Ente004/RobOHMobil-convoy/Dokumentation/KiCad-Pläne/Robomobil_ESP.kicad_sch

## KiCad design Dokumentation/KiCad-Pläne/Robomobil_ESP.kicad_sch (2026-03-16)

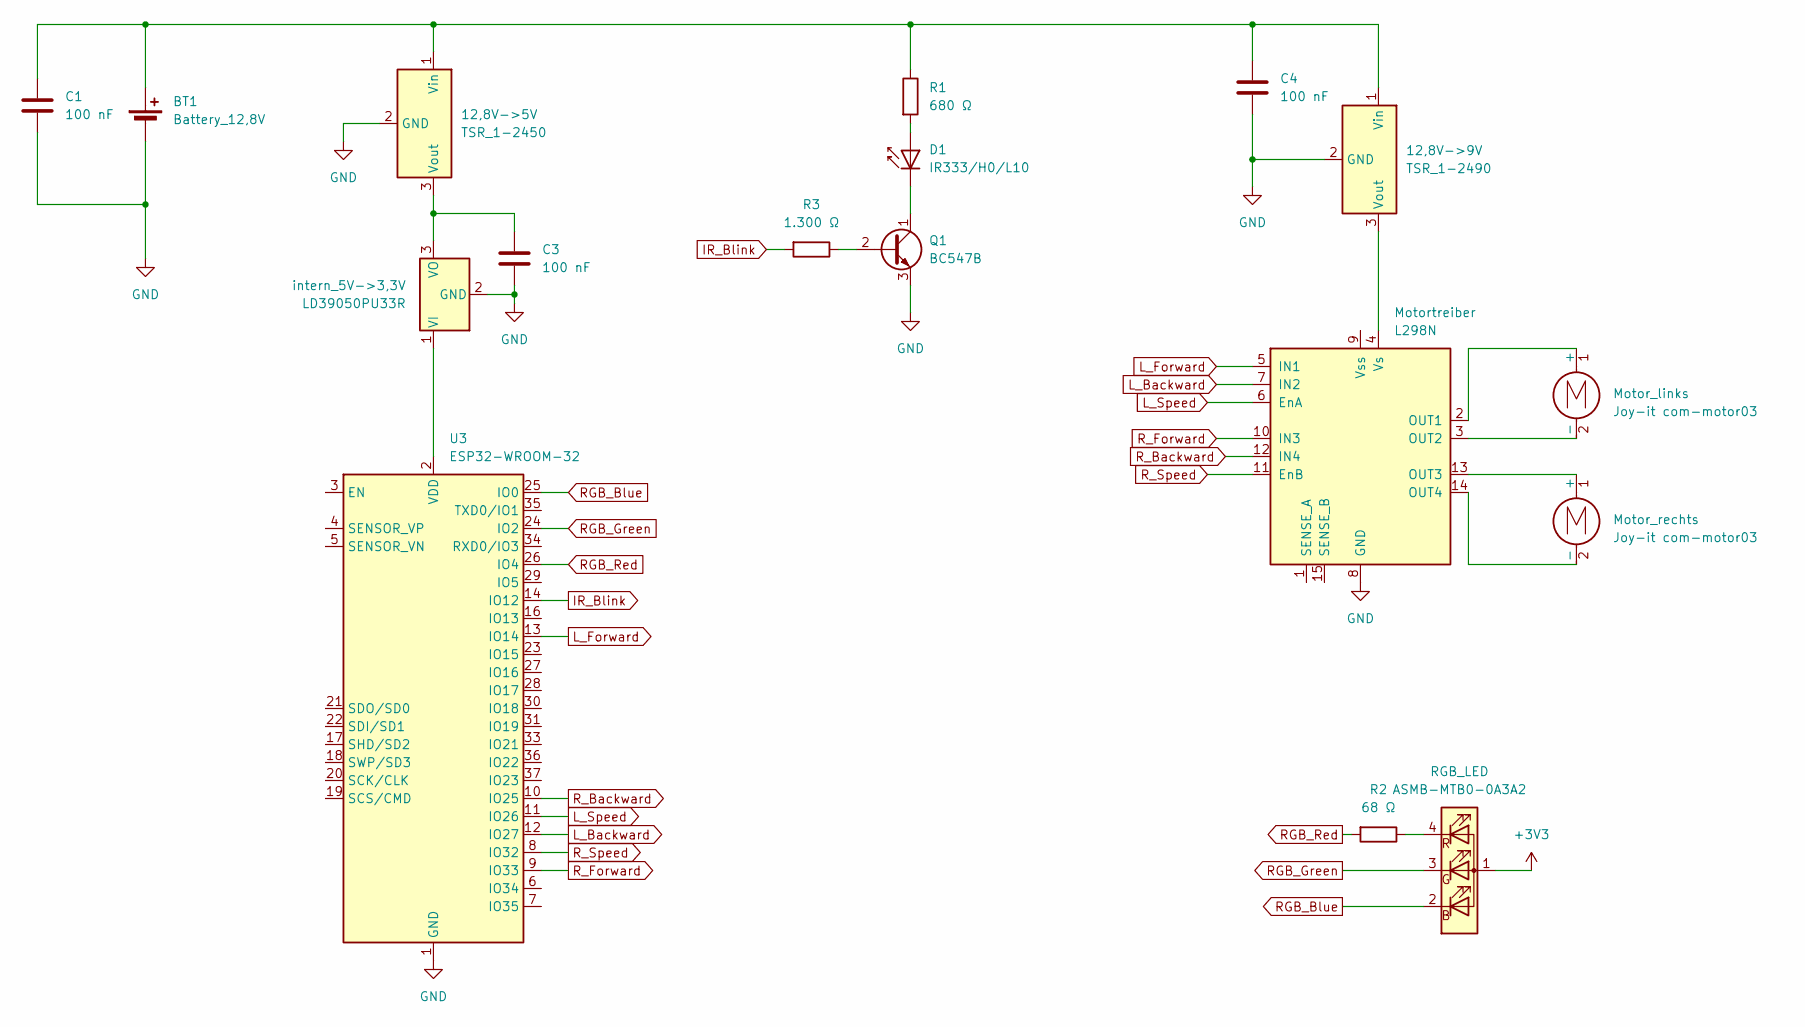
[picture p24: schematic Robomobil_ESP.kicad_sch]

Parts:
12,8V->5V: TSR_1-2450; Converter_DCDC_TRACO_TSR-1_THT
12,8V->9V: TSR_1-2490; Converter_DCDC_TRACO_TSR-1_THT
BT1: Battery_12,8V
C1, C3, C4: 100 nF
D1: IR333/H0/L10; LED_D5.0mm_IRGrey
Motor_links: Joy-it com-motor03
Motor_rechts: Joy-it com-motor03
Motortreiber: L298N; TO-220-15_P2.54x2.54mm_StaggerOdd_Lead4.58mm_Vertical
Q1: BC547B; TO-92_Inline
R1: 680 Ω
R2: 68 Ω
R3: 1.300 Ω
RGB_LED: ASMB-MTB0-0A3A2; LED_Avago_PLCC4_3.2x2.8mm_CW
U3: ESP32-WROOM-32
intern_5V->3,3V: LD39050PU33R; TO-252-3_TabPin2

Connections:
+3V3: RGB_LED.1 (A)
GND: 12,8V->5V.2 (GND), 12,8V->9V.2 (GND), BT1.2 (-), C1.2, C3.2, C4.2, Motortreiber.8 (GND), Q1.3 (E), U3.1 (GND), U3.15 (GND), U3.38 (GND), U3.39 (GND), intern_5V->3,3V.2 (GND)
IR_Blink: R3.2, U3.14 (IO12)
L_Backward: Motortreiber.7 (IN2), U3.12 (IO27)
L_Forward: Motortreiber.5 (IN1), U3.13 (IO14)
L_Speed: Motortreiber.6 (EnA), U3.11 (IO26)
unnamed: 12,8V->5V.1 (Vin), 12,8V->9V.1 (Vin), BT1.1 (+), C1.1, C4.1, R1.1
unnamed: 12,8V->5V.3 (Vout), C3.1, intern_5V->3,3V.3 (VO)
unnamed: 12,8V->9V.3 (Vout), Motortreiber.4 (Vs)
unnamed: D1.1 (K), Q1.1 (C)
unnamed: D1.2 (A), R1.2
unnamed: Motor_links.1 (+), Motortreiber.2 (OUT1)
unnamed: Motor_links.2 (-), Motortreiber.3 (OUT2)
unnamed: Motor_rechts.1 (+), Motortreiber.13 (OUT3)
unnamed: Motor_rechts.2 (-), Motortreiber.14 (OUT4)
unnamed: Q1.2 (B), R3.1
unnamed: R2.1, RGB_LED.4 (RK)
unnamed: U3.2 (VDD), intern_5V->3,3V.1 (VI)
RGB_Blue: RGB_LED.2 (BK), U3.25 (IO0)
RGB_Green: RGB_LED.3 (GK), U3.24 (IO2)
RGB_Red: R2.2, U3.26 (IO4)
R_Backward: Motortreiber.12 (IN4), U3.10 (IO25)
R_Forward: Motortreiber.10 (IN3), U3.9 (IO33)
R_Speed: Motortreiber.11 (EnB), U3.8 (IO32)
