Ente004/RobOHMobil-convoy/Dokumentation/KiCad-Pläne/Robomobil_STM.kicad_sch

## KiCad design Dokumentation/KiCad-Pläne/Robomobil_STM.kicad_sch (2026-03-16)

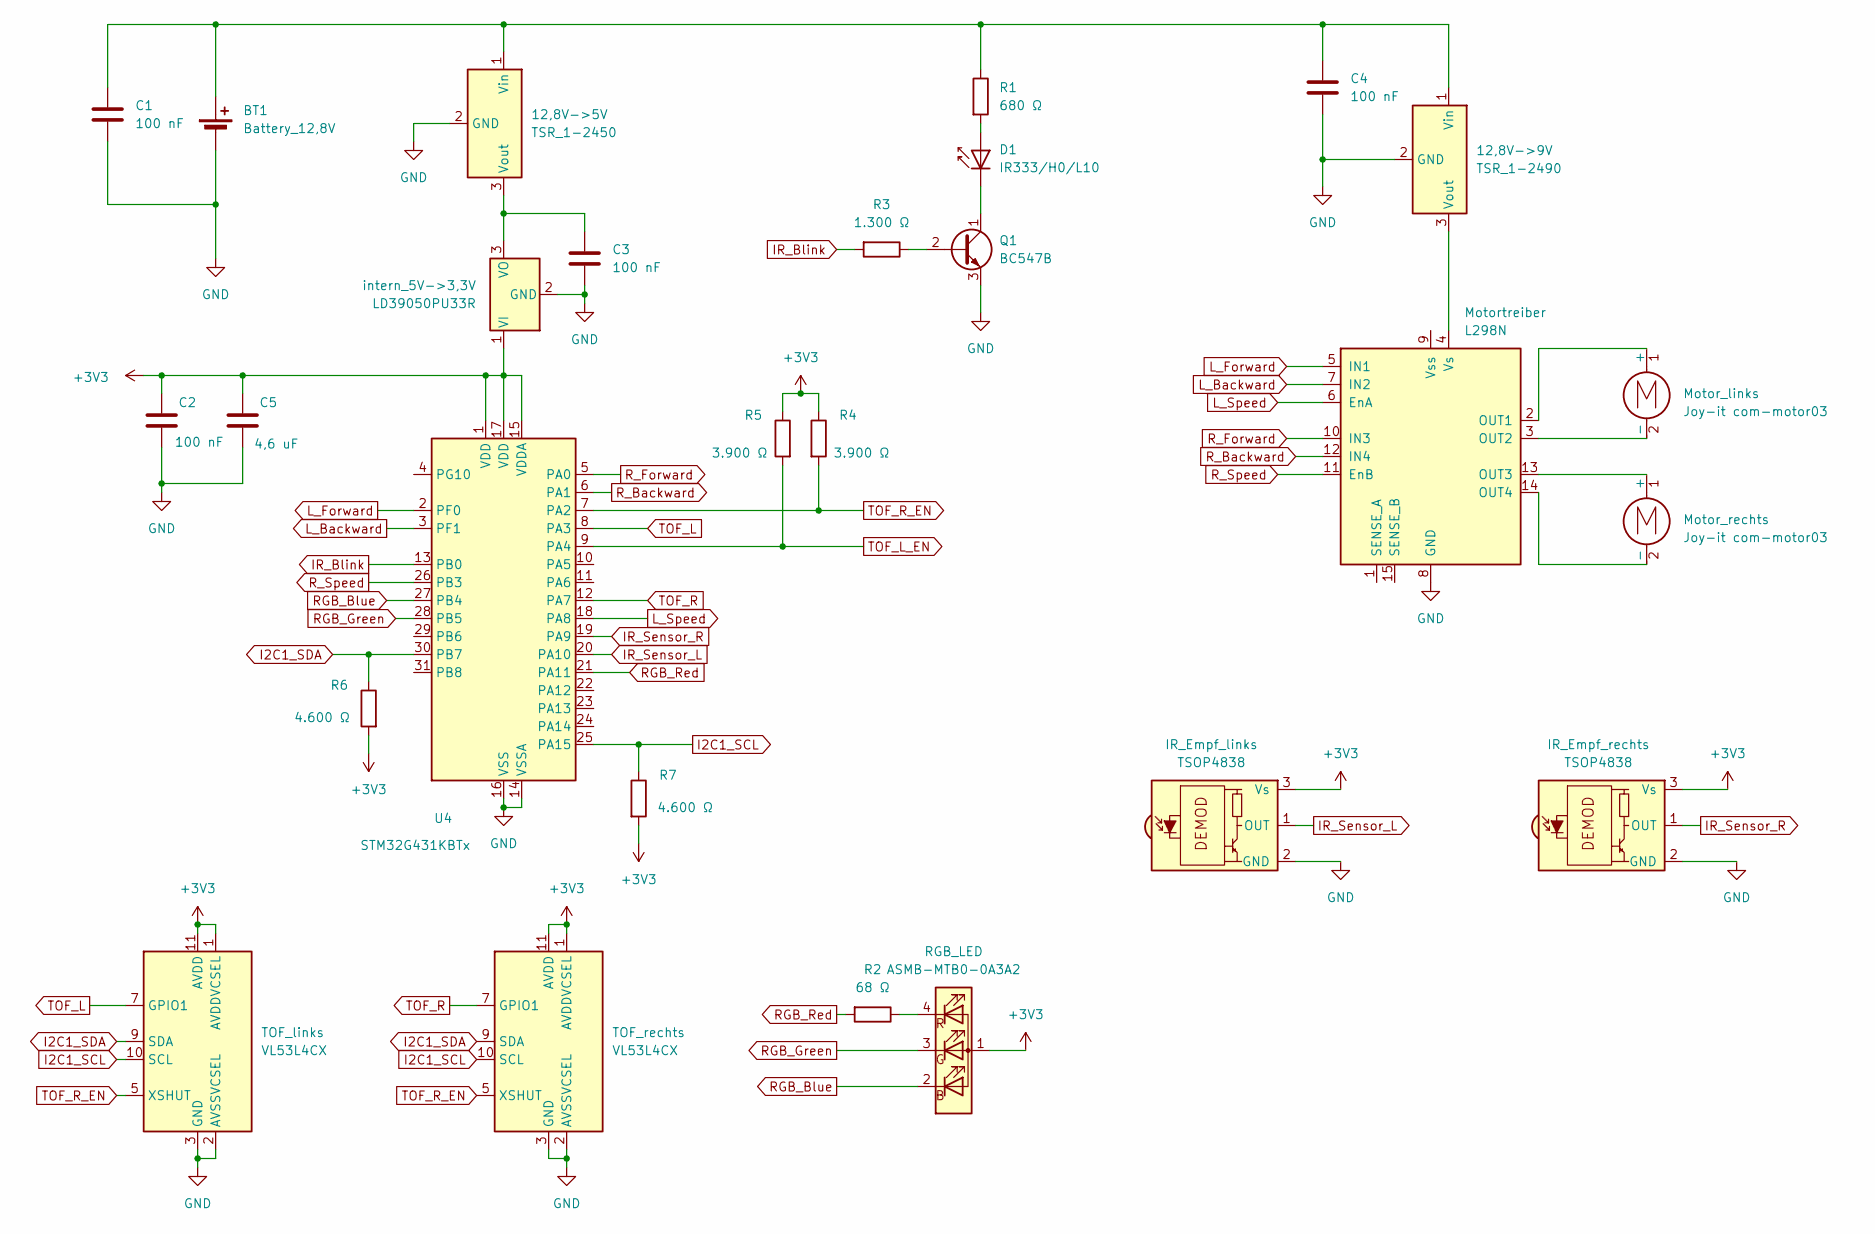
[picture p25: schematic Robomobil_STM.kicad_sch]

Parts:
12,8V->5V: TSR_1-2450; Converter_DCDC_TRACO_TSR-1_THT
12,8V->9V: TSR_1-2490; Converter_DCDC_TRACO_TSR-1_THT
BT1: Battery_12,8V
C1, C2, C3, C4: 100 nF
C5: 4,6 uF
D1: IR333/H0/L10; LED_D5.0mm_IRGrey
IR_Empf_links: TSOP4838; Vishay_MINIMOLD-3Pin
IR_Empf_rechts: TSOP4838; Vishay_MINIMOLD-3Pin
Motor_links: Joy-it com-motor03
Motor_rechts: Joy-it com-motor03
Motortreiber: L298N; TO-220-15_P2.54x2.54mm_StaggerOdd_Lead4.58mm_Vertical
Q1: BC547B; TO-92_Inline
R1: 680 Ω
R2: 68 Ω
R3: 1.300 Ω
R4, R5: 3.900 Ω
R6, R7: 4.600 Ω
RGB_LED: ASMB-MTB0-0A3A2; LED_Avago_PLCC4_3.2x2.8mm_CW
TOF_links: VL53L4CX; ST_VL53L1x
TOF_rechts: VL53L4CX; ST_VL53L1x
U4: STM32G431KBTx; LQFP-32_7x7mm_P0.8mm
intern_5V->3,3V: LD39050PU33R; TO-252-3_TabPin2

Connections:
+3V3: C2.1, C5.1, IR_Empf_links.3 (Vs), IR_Empf_rechts.3 (Vs), R4.1, R5.1, R6.2, R7.2, RGB_LED.1 (A), TOF_links.1 (AVDDVCSEL), TOF_links.11 (AVDD), TOF_rechts.1 (AVDDVCSEL), TOF_rechts.11 (AVDD), U4.1 (VDD), U4.15 (VDDA), U4.17 (VDD), intern_5V->3,3V.1 (VI)
GND: 12,8V->5V.2 (GND), 12,8V->9V.2 (GND), BT1.2 (-), C1.2, C2.2, C3.2, C4.2, C5.2, IR_Empf_links.2 (GND), IR_Empf_rechts.2 (GND), Motortreiber.8 (GND), Q1.3 (E), TOF_links.2 (AVSSVCSEL), TOF_links.3 (GND), TOF_links.4 (GND), TOF_links.6 (GND), TOF_links.12 (GND), TOF_rechts.2 (AVSSVCSEL), TOF_rechts.3 (GND), TOF_rechts.4 (GND), TOF_rechts.6 (GND), TOF_rechts.12 (GND), U4.14 (VSSA), U4.16 (VSS), U4.32 (VSS), intern_5V->3,3V.2 (GND)
I2C1_SCL: R7.1, TOF_links.10 (SCL), TOF_rechts.10 (SCL), U4.25 (PA15)
I2C1_SDA: R6.1, TOF_links.9 (SDA), TOF_rechts.9 (SDA), U4.30 (PB7)
IR_Blink: R3.2, U4.13 (PB0)
IR_Sensor_L: IR_Empf_links.1 (OUT), U4.20 (PA10)
IR_Sensor_R: IR_Empf_rechts.1 (OUT), U4.19 (PA9)
L_Backward: Motortreiber.7 (IN2), U4.3 (PF1)
L_Forward: Motortreiber.5 (IN1), U4.2 (PF0)
L_Speed: Motortreiber.6 (EnA), U4.18 (PA8)
unnamed: 12,8V->5V.1 (Vin), 12,8V->9V.1 (Vin), BT1.1 (+), C1.1, C4.1, R1.1
unnamed: 12,8V->5V.3 (Vout), C3.1, intern_5V->3,3V.3 (VO)
unnamed: 12,8V->9V.3 (Vout), Motortreiber.4 (Vs)
unnamed: D1.1 (K), Q1.1 (C)
unnamed: D1.2 (A), R1.2
unnamed: Motor_links.1 (+), Motortreiber.2 (OUT1)
unnamed: Motor_links.2 (-), Motortreiber.3 (OUT2)
unnamed: Motor_rechts.1 (+), Motortreiber.13 (OUT3)
unnamed: Motor_rechts.2 (-), Motortreiber.14 (OUT4)
unnamed: Q1.2 (B), R3.1
unnamed: R2.1, RGB_LED.4 (RK)
RGB_Blue: RGB_LED.2 (BK), U4.27 (PB4)
RGB_Green: RGB_LED.3 (GK), U4.28 (PB5)
RGB_Red: R2.2, U4.21 (PA11)
R_Backward: Motortreiber.12 (IN4), U4.6 (PA1)
R_Forward: Motortreiber.10 (IN3), U4.5 (PA0)
R_Speed: Motortreiber.11 (EnB), U4.26 (PB3)
TOF_L: TOF_links.7 (GPIO1), U4.8 (PA3)
TOF_L_EN: R5.2, U4.9 (PA4)
TOF_R: TOF_rechts.7 (GPIO1), U4.12 (PA7)
TOF_R_EN: R4.2, TOF_links.5 (XSHUT), TOF_rechts.5 (XSHUT), U4.7 (PA2)
